Lee-Kevin/X_Light_Project/LightControl_Master/logo.h

#ifndef _LOGO_H
#define _LOGO_H

const unsigned char SeeedLogo[] PROGMEM ={
0x00, 0x00, 0x00, 0x00, 0x00, 0x00, 0x00, 0x00, 0x80, 0x00, 0x00, 0x00, 0x00, 0x00, 0x00, 0x80,
0x00, 0x00, 0x00, 0x00, 0x00, 0x00, 0x00, 0x00, 0x00, 0x00, 0x00, 0x00, 0x00, 0x00, 0x00, 0x00,
0x00, 0x00, 0x00, 0x00, 0x00, 0x00, 0x00, 0x00, 0x00, 0x00, 0x00, 0x00, 0x00, 0x00, 0x00, 0x00,
0x00, 0x00, 0x00, 0x00, 0x00, 0x00, 0x00, 0x00, 0x00, 0x00, 0x00, 0x00, 0x00, 0x00, 0x00, 0x00,
0x00, 0x00, 0x00, 0x00, 0x00, 0x00, 0x00, 0x00, 0x00, 0x00, 0x00, 0x00, 0x00, 0x00, 0x00, 0x00,
0x00, 0x00, 0x00, 0x00, 0x00, 0x00, 0x00, 0x00, 0x00, 0x00, 0x00, 0x00, 0x00, 0x00, 0x00, 0x00,
0x00, 0x00, 0x00, 0x00, 0x00, 0x00, 0x00, 0x00, 0x00, 0x00, 0x00, 0x00, 0x00, 0x00, 0x00, 0x00,
0x00, 0x00, 0x00, 0x00, 0x00, 0x00, 0x00, 0x00, 0x00, 0x00, 0x00, 0x00, 0x00, 0x00, 0x00, 0x00,
0x60, 0xf0, 0xc0, 0x00, 0x00, 0x00, 0xfc, 0xff, 0x87, 0x00, 0x00, 0x00, 0x00, 0x00, 0x00, 0x03,
0xff, 0xfc, 0x00, 0x00, 0x00, 0x80, 0xf0, 0x20, 0x00, 0x00, 0x80, 0xc0, 0xc0, 0x60, 0xe0, 0xc0,
0xc0, 0x00, 0x00, 0x00, 0xc0, 0xc0, 0xc0, 0x60, 0xe0, 0xc0, 0xc0, 0x80, 0x00, 0x00, 0x80, 0xc0,
0xc0, 0xe0, 0x60, 0xc0, 0xc0, 0x80, 0x00, 0x00, 0x00, 0xc0, 0xc0, 0xc0, 0x60, 0xe0, 0xc0, 0xc0,
0x80, 0x00, 0x00, 0x80, 0xc0, 0xc0, 0xe0, 0xe0, 0xc0, 0xc0, 0xf8, 0xf8, 0x00, 0x00, 0x00, 0x00,
0x00, 0xc0, 0xc0, 0xe0, 0x60, 0xc0, 0xc0, 0x80, 0x00, 0xc0, 0xf0, 0xf0, 0xf0, 0xc0, 0x00, 0xc0,
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
0x00,0x00,0x00,0x00,0x00,0x00,0x00,0x00,0x00,0x00,0x00,0x00,0x00,0x00,0x00,0x00,
0x00,0x00,0x00,0x00,0x00,0x00,0x00,0x00,0x00,0x00,0x00,0x00,0x00,0x00,0x00,0x00,
0x00,0x00,0x00,0x00,0x00,0x00,0x00,0x00,0x00,0x00,0x00,0x00,0x00,0x00,0x00,0x00,
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
};


#endif
